saidlm/Turnstile_antenna_403-435_MHz/images/20220118_143512.jpg

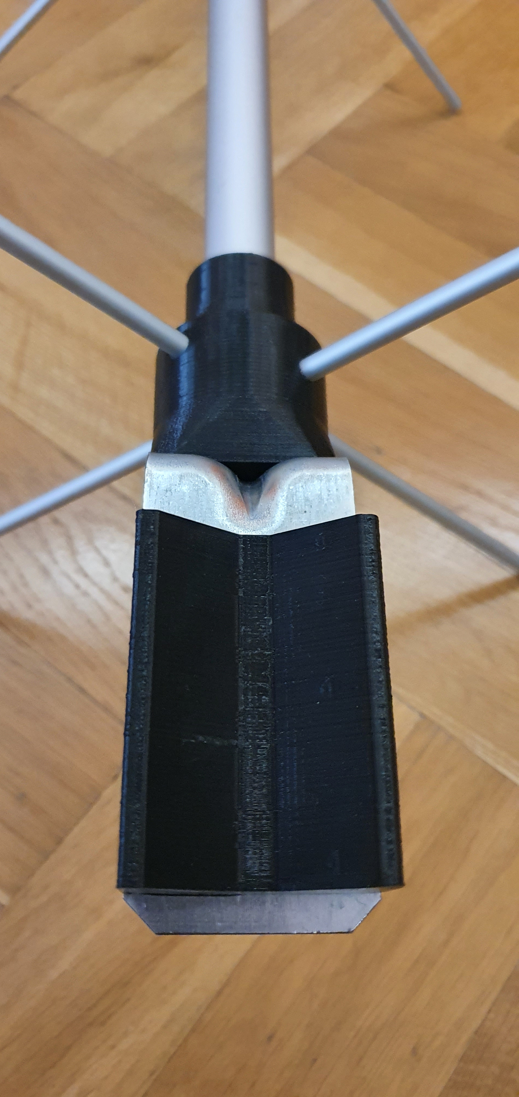
images/20220118_143512.jpg
