saidlm/Turnstile_antenna_403-435_MHz/images/20220118_165315.jpg

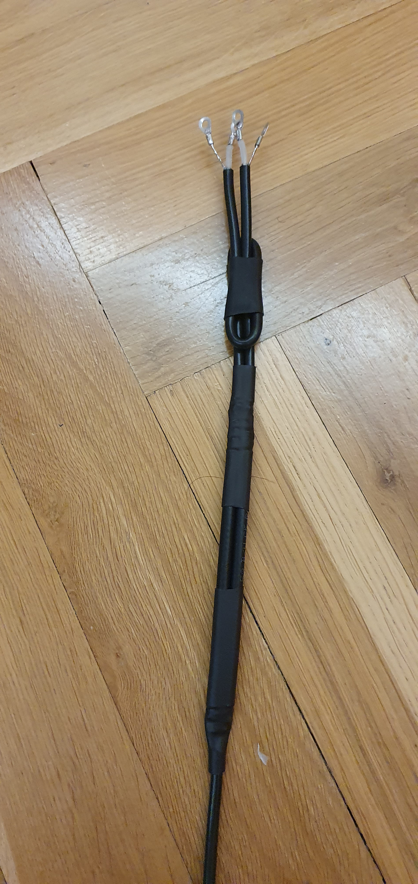
images/20220118_165315.jpg
