saidlm/Turnstile_antenna_403-435_MHz/images/20220120_180736.jpg

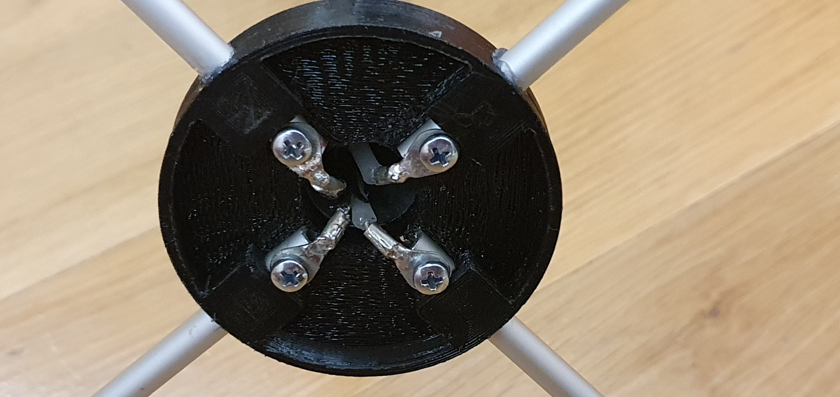
images/20220120_180736.jpg
