saidlm/Turnstile_antenna_403-435_MHz/images/20220124_175721.jpg

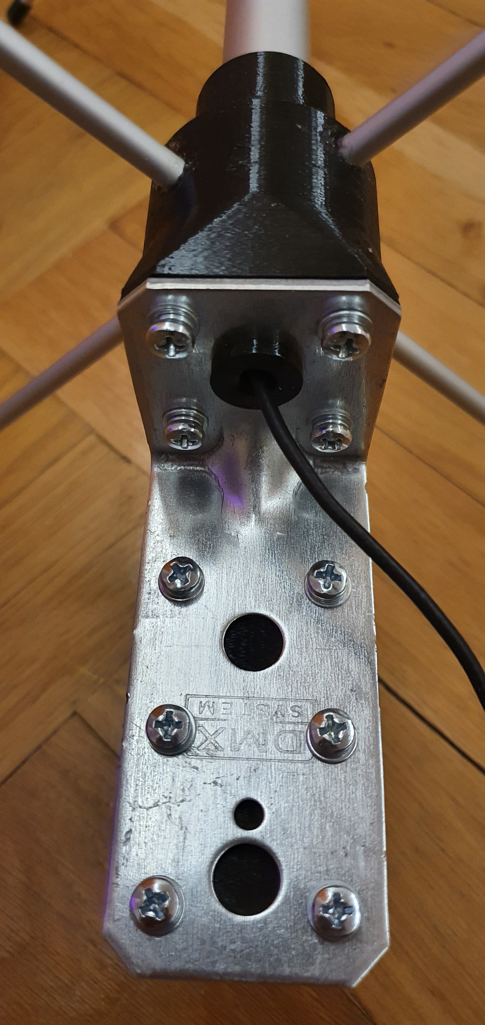
images/20220124_175721.jpg
