saidlm/Turnstile_antenna_403-435_MHz/images/20220124_175746.jpg

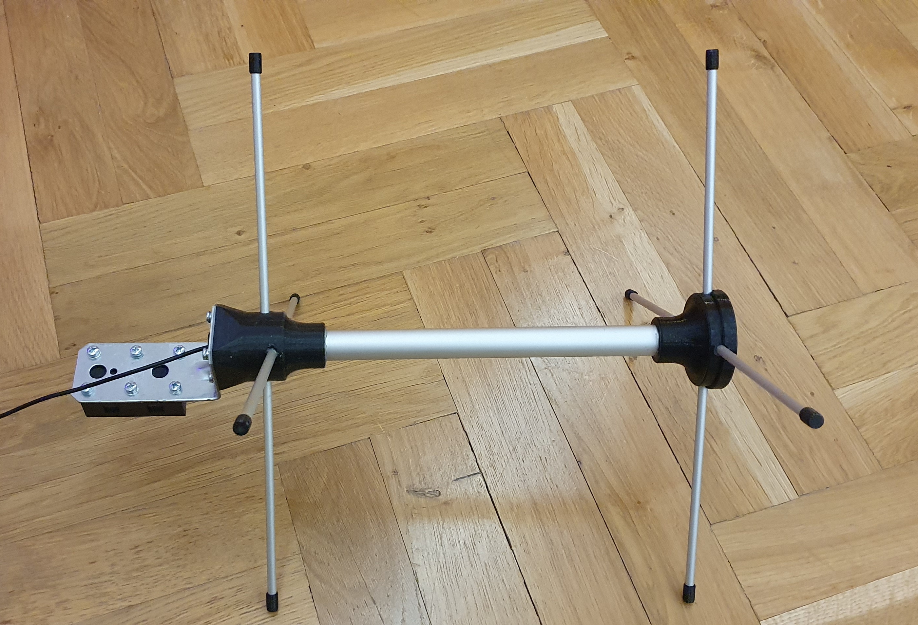
images/20220124_175746.jpg
